AethelVeritas/Quaero/pics/pic_8.png

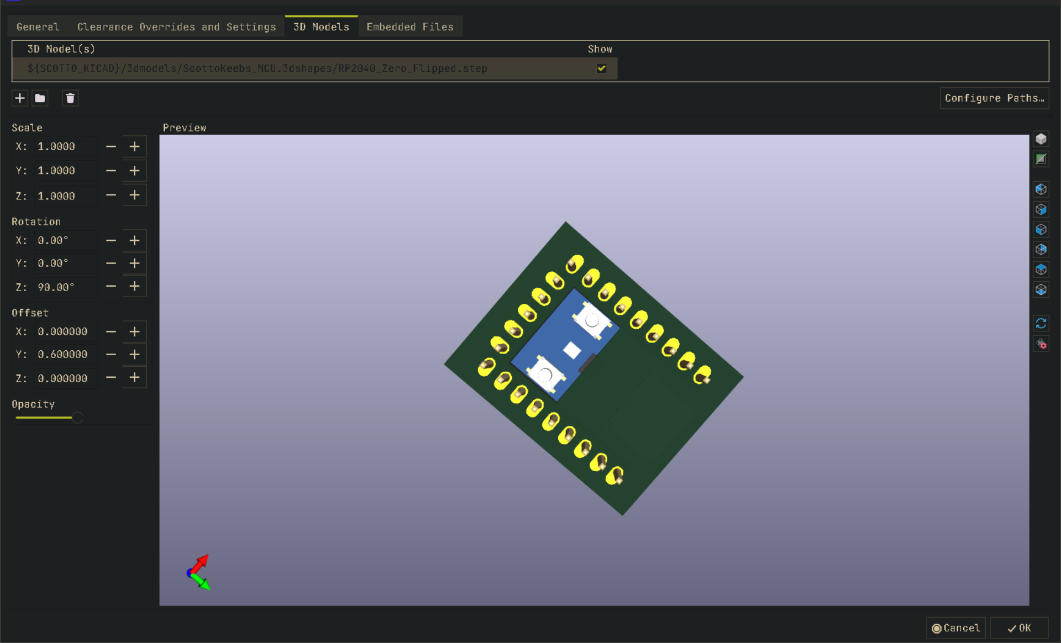
pics/pic_8.png
